esheffield/m0110a-atmega32/include/M0110aKeyboard.hpp

#include <Arduino.h>

#ifndef M0110AKEYBOARD_HPP
#define M0110AKEYBOARD_HPP

#define MODEL_ID 0x0B
#define KB_ACK 0x7D
#define KB_NAK 0x77
#define KB_NULL 0x7B
#define KP_MOD 0x79

#define KEY_NONE 0x00
#define KEY_TXN_UP 0x80

#define CMD_MODEL 0x16
#define CMD_INQUIRY 0x10
#define CMD_INSTANT 0x14
#define CMD_TEST 0x36

#define KEY_GRAVE 0x65
#define KEY_1 0x25
#define KEY_2 0x27
#define KEY_3 0x29
#define KEY_4 0x2B
#define KEY_5 0x2F
#define KEY_6 0x2D
#define KEY_7 0x35
#define KEY_8 0x39
#define KEY_9 0x33
#define KEY_0 0x3B
#define KEY_MINUS 0x37
#define KEY_EQUAL 0x31
#define KEY_BS 0x67
#define KEY_TAB 0x61
#define KEY_Q 0x19
#define KEY_W 0x1B
#define KEY_E 0x1D
#define KEY_R 0x1F
#define KEY_T 0x23
#define KEY_Y 0x21
#define KEY_U 0x41
#define KEY_I 0x45
#define KEY_O 0x3F
#define KEY_P 0x47
#define KEY_LBKT 0x43
#define KEY_RBKT 0x3D
#define KEY_LOCK 0x73
#define KEY_A 0x01
#define KEY_S 0x03
#define KEY_D 0x05
#define KEY_F 0x07
#define KEY_G 0x0B
#define KEY_H 0x09
#define KEY_J 0x4D
#define KEY_K 0x51
#define KEY_L 0x4B
#define KEY_SEMI 0x53
#define KEY_APOS 0x4F
#define KEY_RETURN 0x49
#define KEY_SHIFT 0x71
#define KEY_Z 0x0D
#define KEY_X 0x0F
#define KEY_C 0x11
#define KEY_V 0x13
#define KEY_B 0x17
#define KEY_N 0x5B
#define KEY_M 0x5D
#define KEY_COMMA 0x57
#define KEY_PERIOD 0x5F
#define KEY_SLASH 0x59
#define KEY_UP 0x1B
#define KEY_OPT 0x75
#define KEY_CMD 0x6F
#define KEY_SPC 0x63
#define KEY_BSLASH 0x55
#define KEY_LEFT 0x0D
#define KEY_RIGHT 0x05
#define KEY_DOWN 0x11
#define KEY_KP_CLR 0x0F
#define KEY_KP_EQUAL 0x11
#define KEY_KP_DIV 0x1B
#define KEY_KP_MUL 0x05
#define KEY_KP_7 0x33
#define KEY_KP_8 0x37
#define KEY_KP_9 0x39
#define KEY_KP_SUB 0x1D
#define KEY_KP_4 0x2D
#define KEY_KP_5 0x2F
#define KEY_KP_6 0x31
#define KEY_KP_ADD 0x0D
#define KEY_KP_1 0x27
#define KEY_KP_2 0x29
#define KEY_KP_3 0x2B
#define KEY_KP_0 0x25
#define KEY_KP_DEC 0x03
#define KEY_KP_ENTER 0x19

#define ROW_COUNT 10
#define COL_COUNT 8
#define MOD_COUNT 4

#define CMD_MASK 0x08
#define OPT_MASK 0x04
#define LCK_MASK 0x02
#define SHF_MASK 0x01

#define CMD_PIN_IDX 0
#define OPT_PIN_IDX 1
#define LCK_PIN_IDX 2
#define SHF_PIN_IDX 3

#define NUMPAD 0x0100
#define NUMPAD2 0x0200

class M0110aKeyboard
{
private:
    byte *row_pins;
    byte *col_pins;
    byte *mod_pins;

    byte key_states[10] = {0, 0, 0, 0, 0, 0, 0, 0, 0, 0};
    byte opt_state = 0;
    byte cmd_state = 0;
    byte lck_state = 0;
    byte shf_state = 0;

    // put function declarations here:

    byte readMods();
    byte readCols();

    bool isKeypad(byte active_row, byte col);
    bool isKeypadShift(byte active_row, byte col);
    byte check_modifier(byte masked_value, byte mod_key_code, byte *state);

public:
    M0110aKeyboard(){};

    void begin(byte *row_pins, byte *col_pins, byte *mod_pins);
    void reset();

    uint16_t getScanCode();
};

const uint16_t KEYPAD_MAP_BY_COL[8] = {
    0,
    0,
    0,
    0,
    0x380,
    0x3FE,
    0x03C,
    0x3F0,
};

const byte KEYMAP[10][8] = {
    {
        KEY_X,
        KEY_GRAVE,
        KEY_TAB,
        KEY_A,
        KEY_SPC,
        KEY_NONE,
        KEY_Z,
        KEY_NONE,
    },
    {
        KEY_C,
        KEY_1,
        KEY_Q,
        KEY_S,
        KEY_NONE,
        KEY_KP_7,
        KEY_NONE,
        KEY_NONE,
    },
    {
        KEY_V,
        KEY_2,
        KEY_W,
        KEY_D,
        KEY_P,
        KEY_KP_8,
        KEY_KP_MUL,
        KEY_NONE,
    },
    {
        KEY_B,
        KEY_3,
        KEY_E,
        KEY_F,
        KEY_LBKT,
        KEY_KP_9,
        KEY_KP_DIV,
        KEY_BSLASH,
    },
    {
        KEY_N,
        KEY_4,
        KEY_R,
        KEY_G,
        KEY_RBKT,
        KEY_KP_SUB,
        KEY_KP_EQUAL,
        KEY_LEFT,
    },
    {
        KEY_M,
        KEY_5,
        KEY_T,
        KEY_H,
        KEY_APOS,
        KEY_UP,
        KEY_KP_CLR,
        KEY_RIGHT,
    },
    {
        KEY_COMMA,
        KEY_6,
        KEY_Y,
        KEY_J,
        KEY_RETURN,
        KEY_KP_1,
        KEY_BS,
        KEY_DOWN,
    },
    {
        KEY_PERIOD,
        KEY_7,
        KEY_U,
        KEY_K,
        KEY_KP_4,
        KEY_KP_2,
        KEY_EQUAL,
        KEY_KP_0,
    },
    {
        KEY_SLASH,
        KEY_8,
        KEY_I,
        KEY_L,
        KEY_KP_5,
        KEY_KP_3,
        KEY_MINUS,
        KEY_KP_DEC,
    },
    {
        KEY_NONE,
        KEY_9,
        KEY_O,
        KEY_SEMI,
        KEY_KP_6,
        KEY_KP_ADD,
        KEY_0,
        KEY_KP_ENTER,
    },
};

#endif
